Dwxing21/esp32-keychain/case/preview_body.png

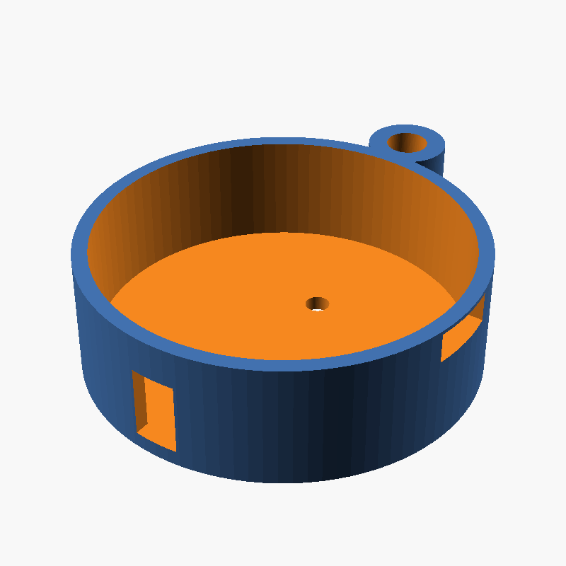
case/preview_body.png
