Dwxing21/esp32-keychain/firmware/previews/screen_lyrics_none.png

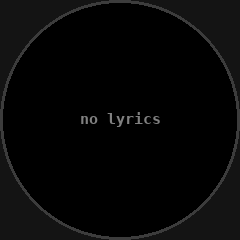
firmware/previews/screen_lyrics_none.png
