Dwxing21/esp32-keychain/firmware/previews/screen_nav_left.png

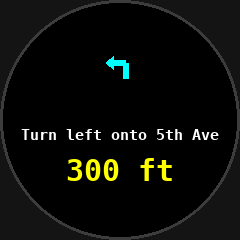
firmware/previews/screen_nav_left.png
