Dwxing21/esp32-keychain/firmware/previews/screen_spotify_paused.png

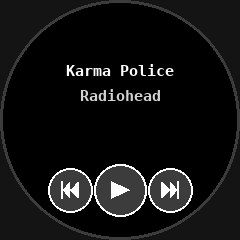
firmware/previews/screen_spotify_paused.png
